subtchallenge/transponder_design/assembly_photos/step_2.jpg

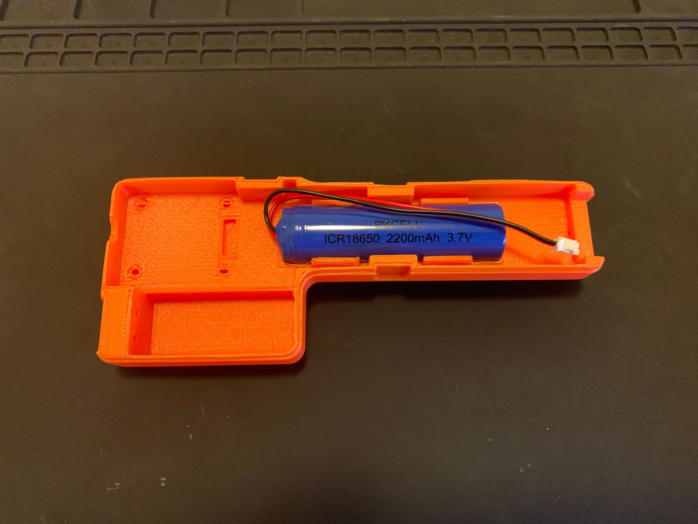
assembly_photos/step_2.jpg
