subtchallenge/transponder_design/assembly_photos/step_3a.jpg

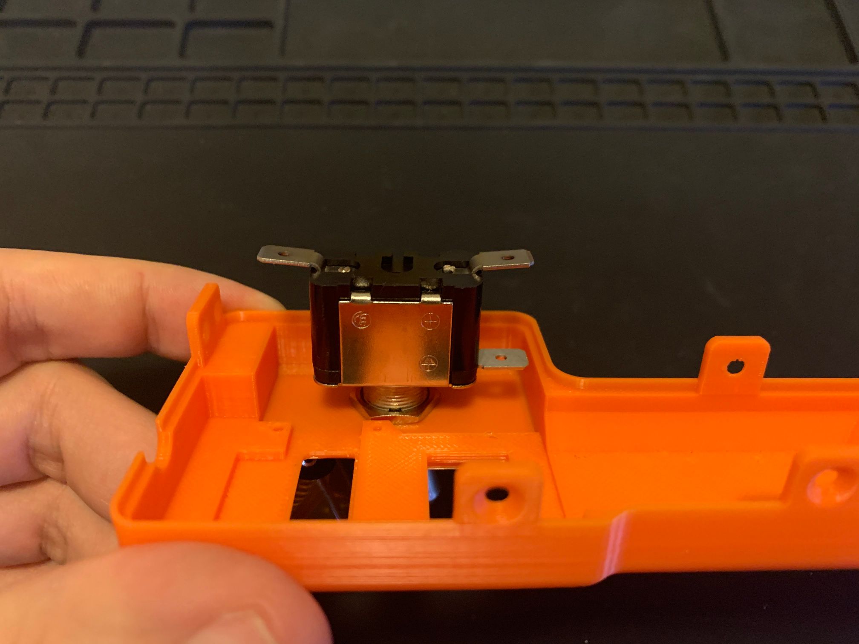
assembly_photos/step_3a.jpg
