subtchallenge/transponder_design/assembly_photos/step_4a.jpg

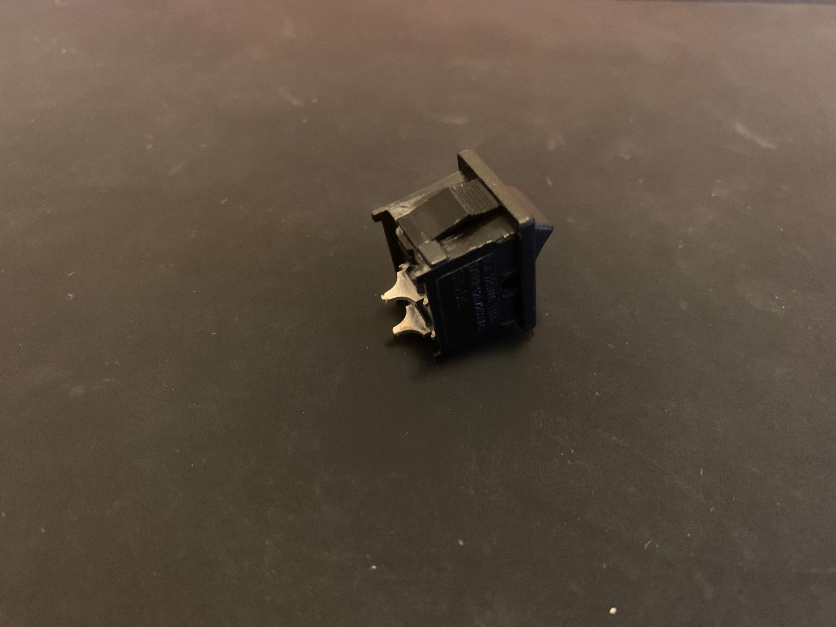
assembly_photos/step_4a.jpg
