subtchallenge/transponder_design/assembly_photos/step_4b.jpg

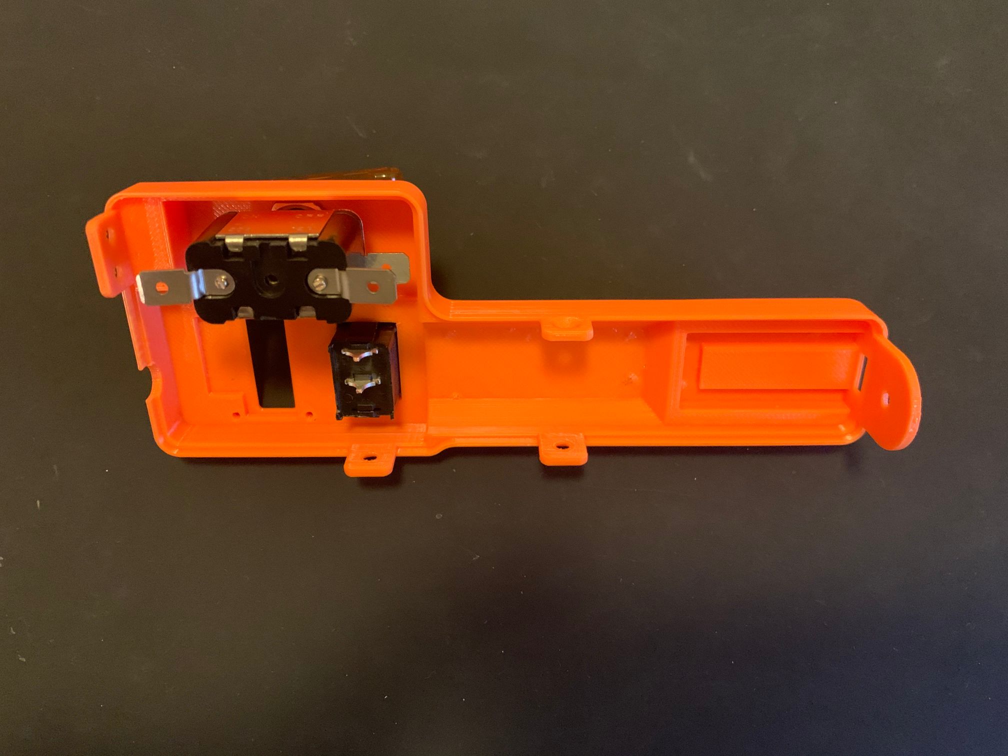
assembly_photos/step_4b.jpg
