subtchallenge/transponder_design/assembly_photos/step_5a.jpg

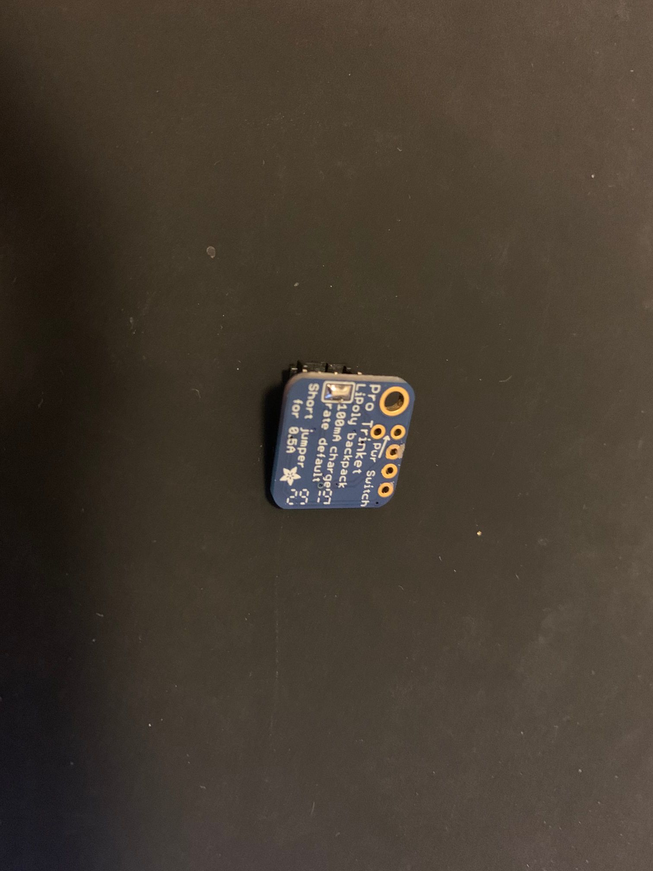
assembly_photos/step_5a.jpg
