subtchallenge/transponder_design/assembly_photos/step_6.jpg

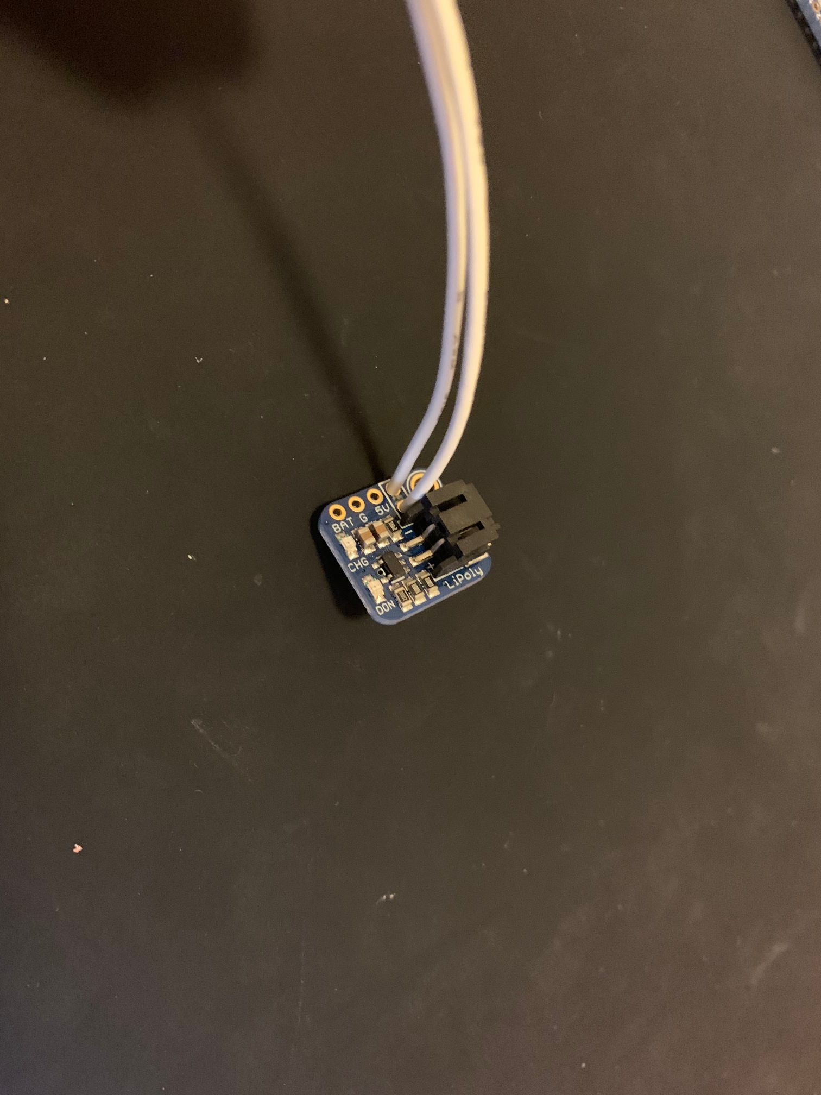
assembly_photos/step_6.jpg
