subtchallenge/transponder_design/assembly_photos/step_7.jpg

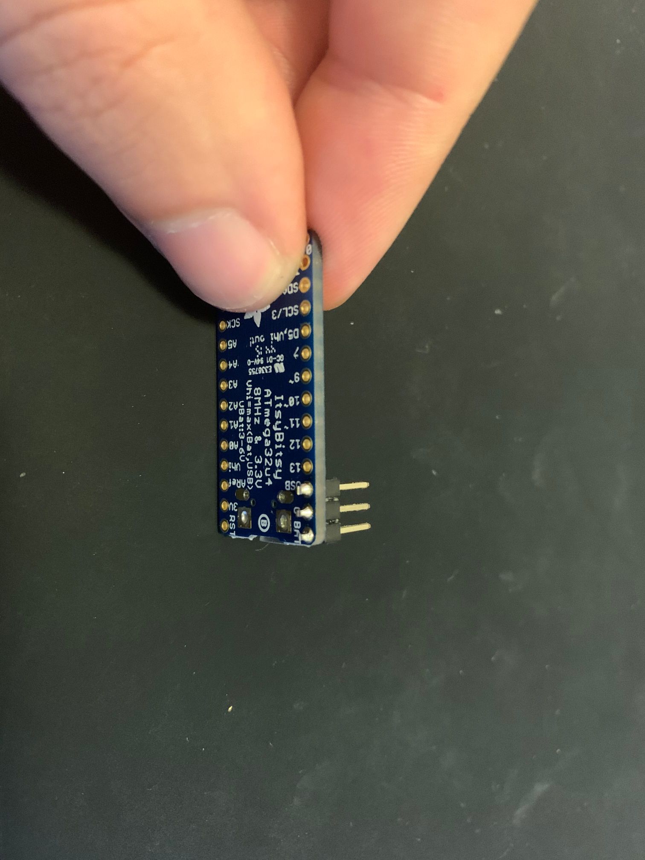
assembly_photos/step_7.jpg
