subtchallenge/transponder_design/assembly_photos/step_8.jpg

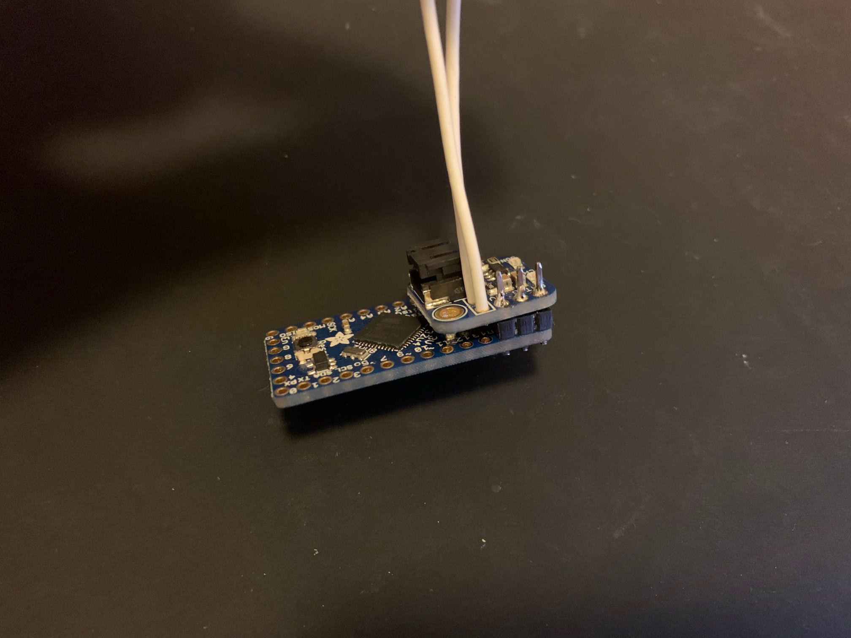
assembly_photos/step_8.jpg
