subtchallenge/transponder_design/assembly_photos/step_9.jpg

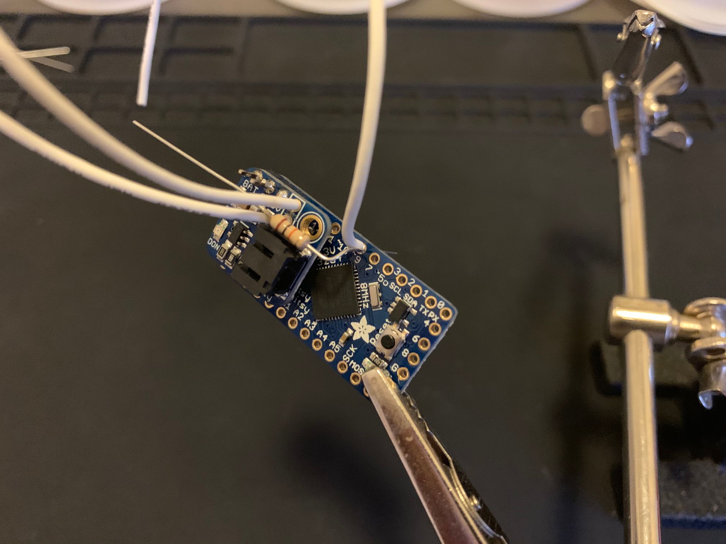
assembly_photos/step_9.jpg
