subtchallenge/transponder_design/assembly_photos/step_10.jpg

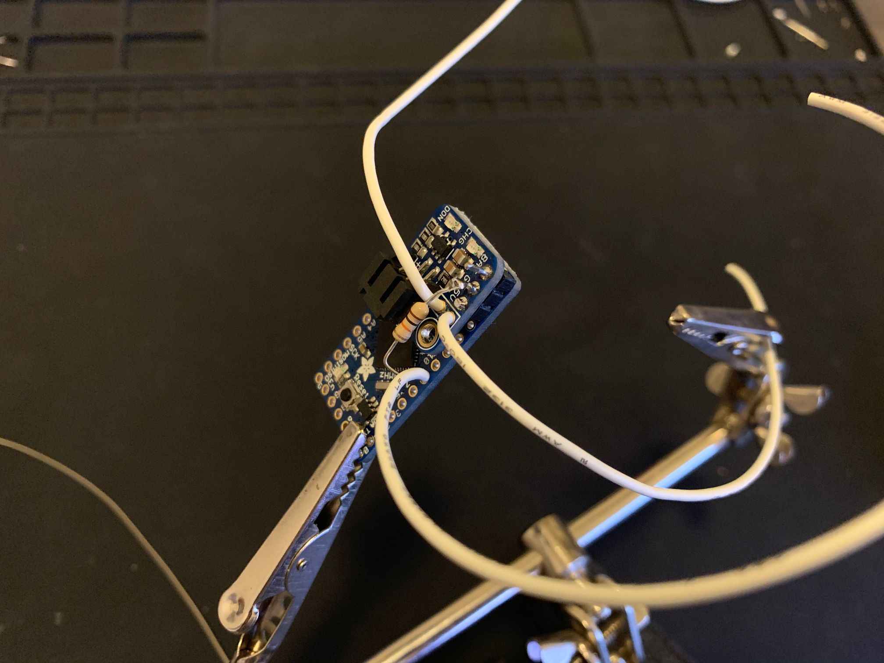
assembly_photos/step_10.jpg
