subtchallenge/transponder_design/assembly_photos/step_11.jpg

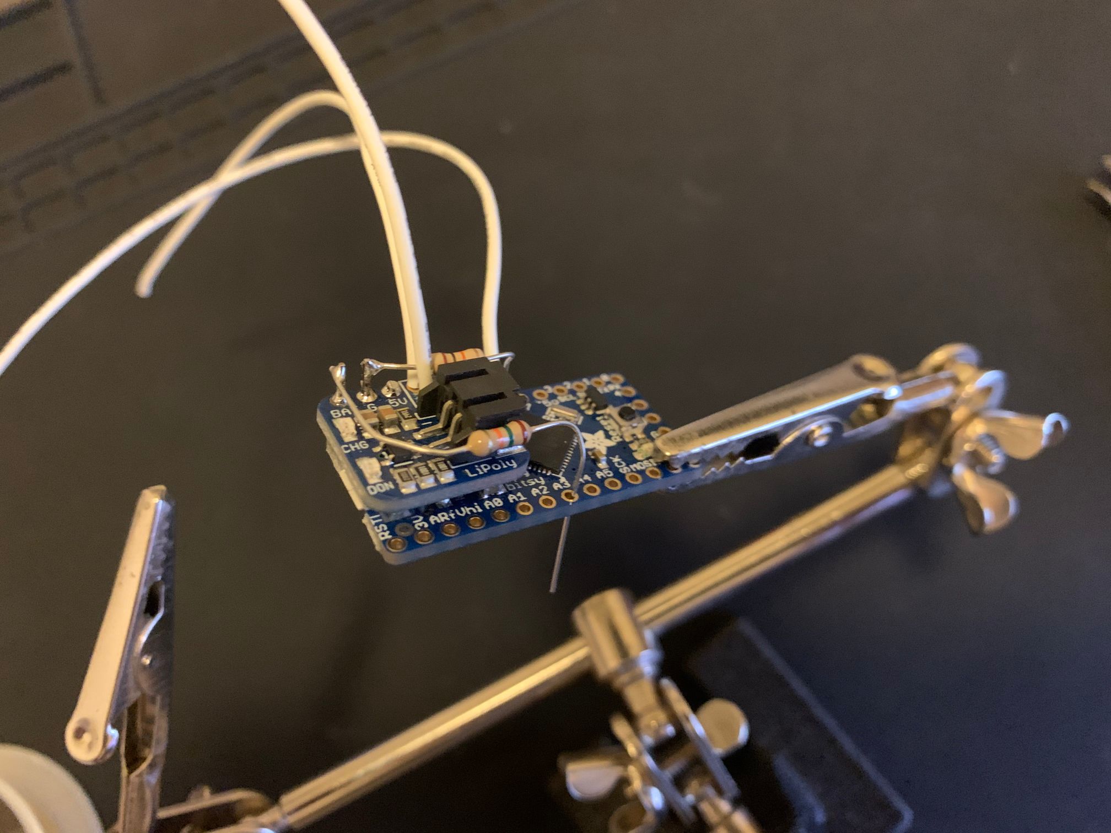
assembly_photos/step_11.jpg
