subtchallenge/transponder_design/assembly_photos/step_12.jpg

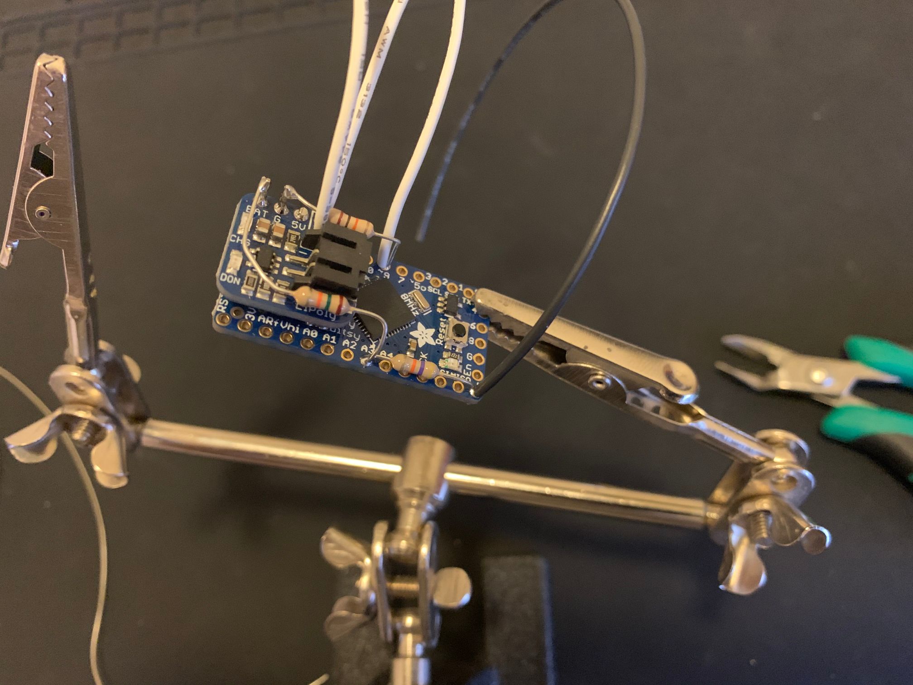
assembly_photos/step_12.jpg
