subtchallenge/transponder_design/assembly_photos/step_13.jpg

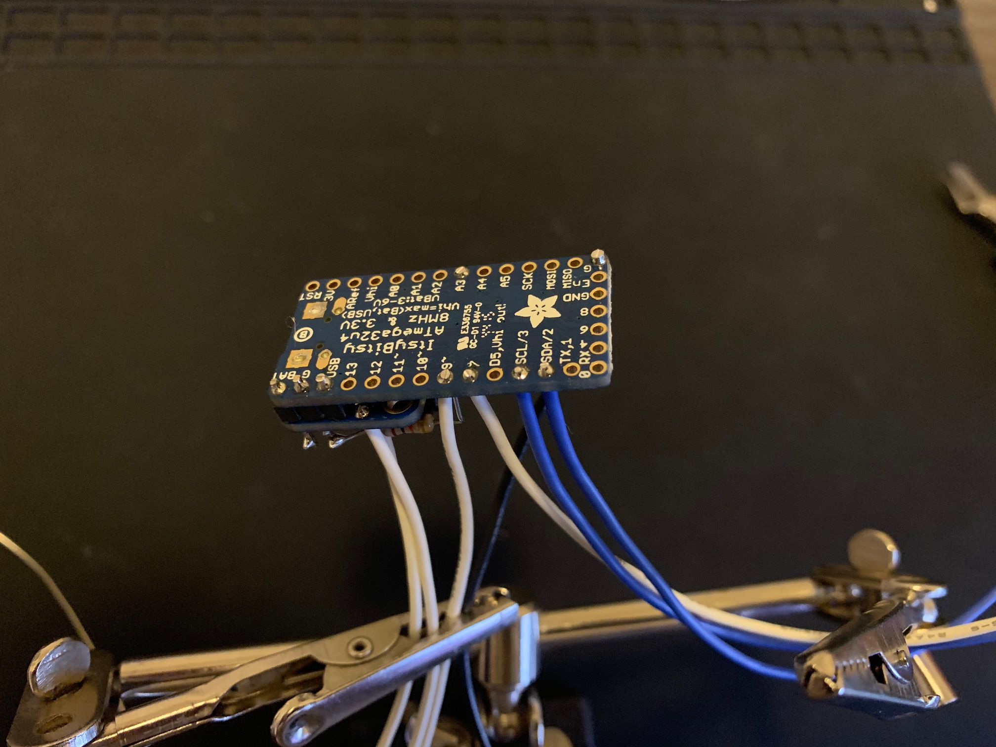
assembly_photos/step_13.jpg
