subtchallenge/transponder_design/assembly_photos/step_14.jpg

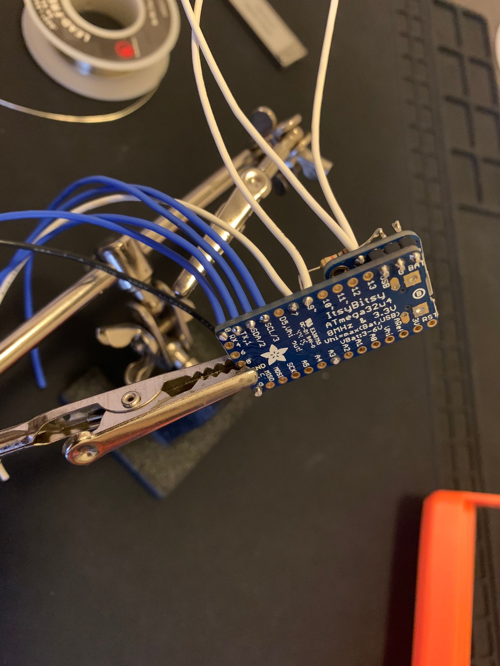
assembly_photos/step_14.jpg
