subtchallenge/transponder_design/assembly_photos/step_15.jpg

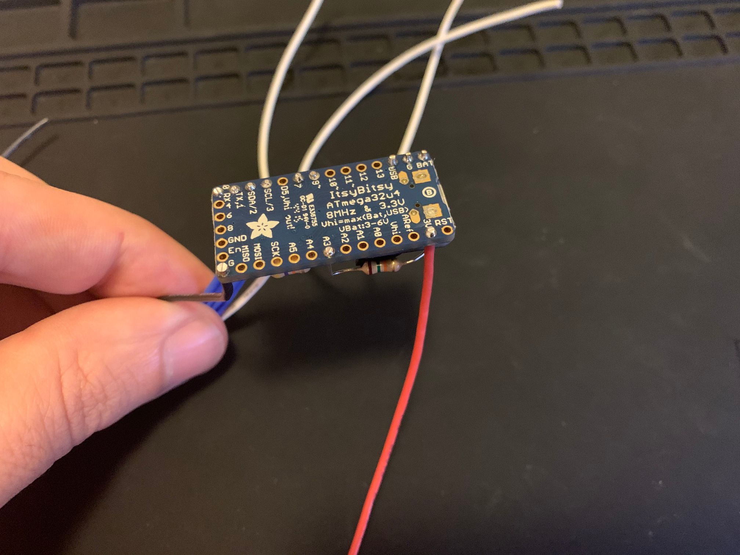
assembly_photos/step_15.jpg
