subtchallenge/transponder_design/assembly_photos/step_16.jpg

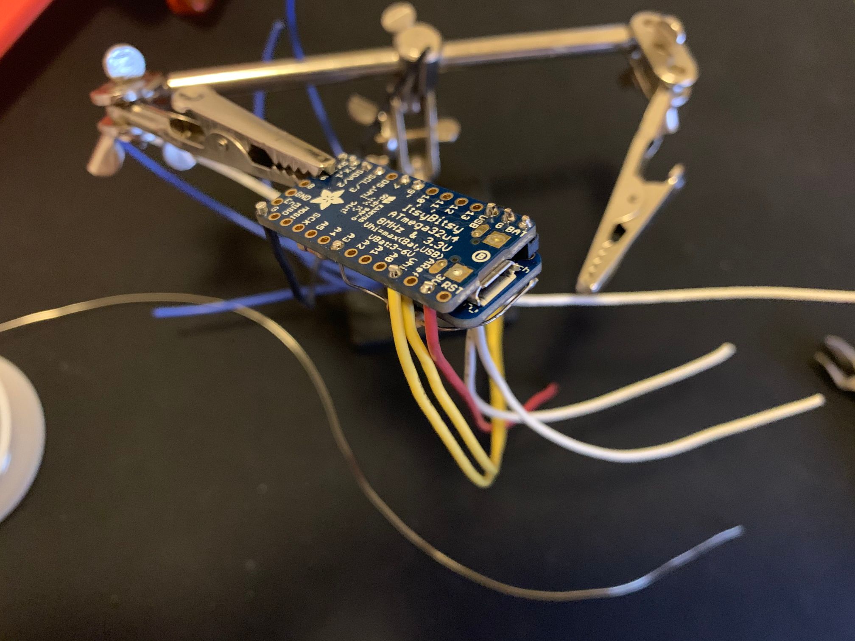
assembly_photos/step_16.jpg
