subtchallenge/transponder_design/assembly_photos/step_18.jpg

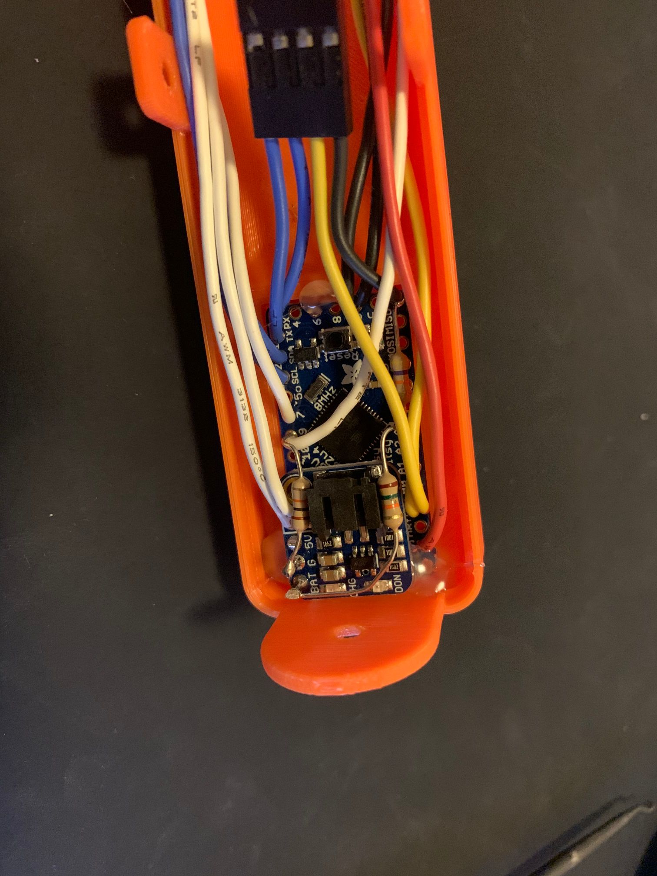
assembly_photos/step_18.jpg
