subtchallenge/transponder_design/assembly_photos/step_19.jpg

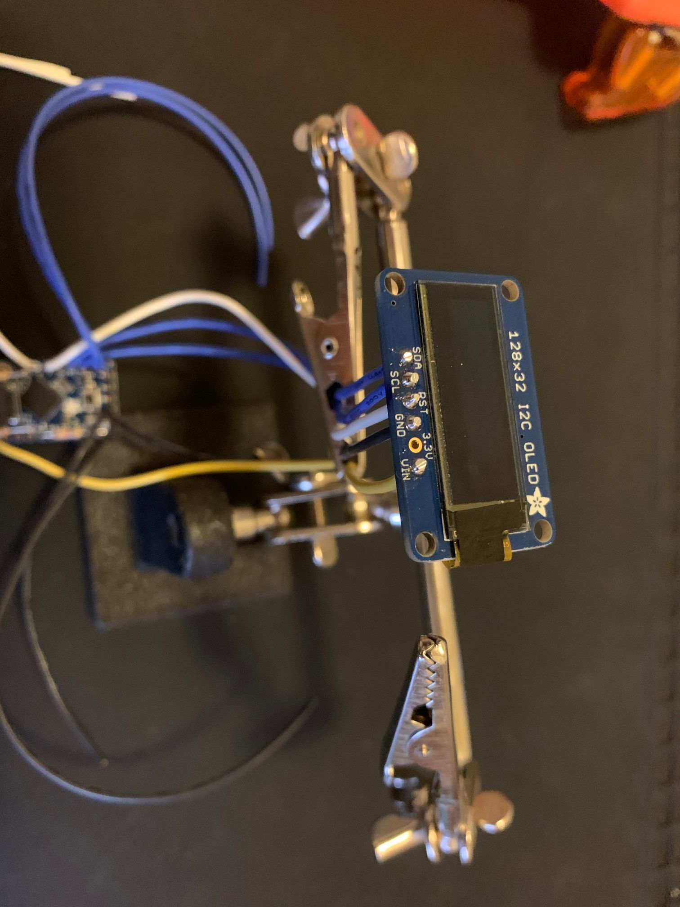
assembly_photos/step_19.jpg
