subtchallenge/transponder_design/assembly_photos/step_21.jpg

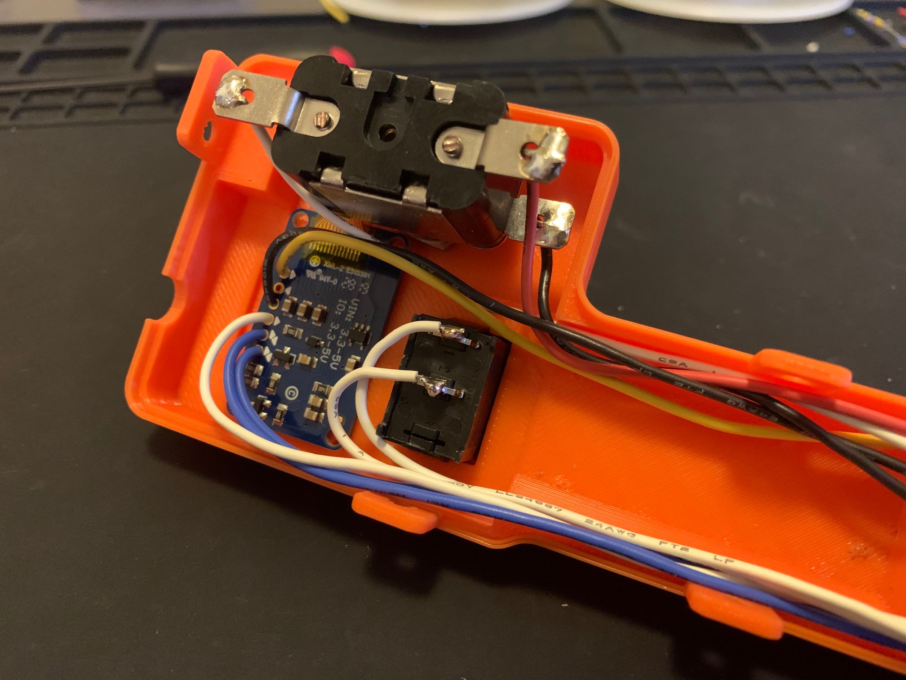
assembly_photos/step_21.jpg
