subtchallenge/transponder_design/assembly_photos/step_22.jpg

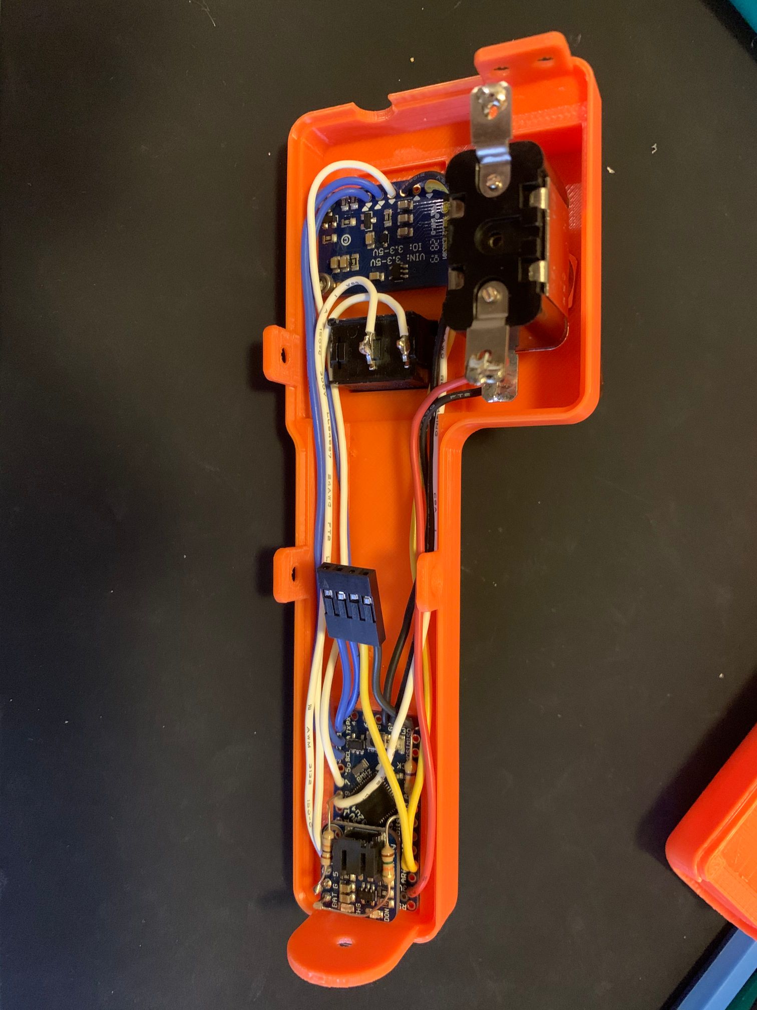
assembly_photos/step_22.jpg
