subtchallenge/transponder_design/assembly_photos/step_23.jpg

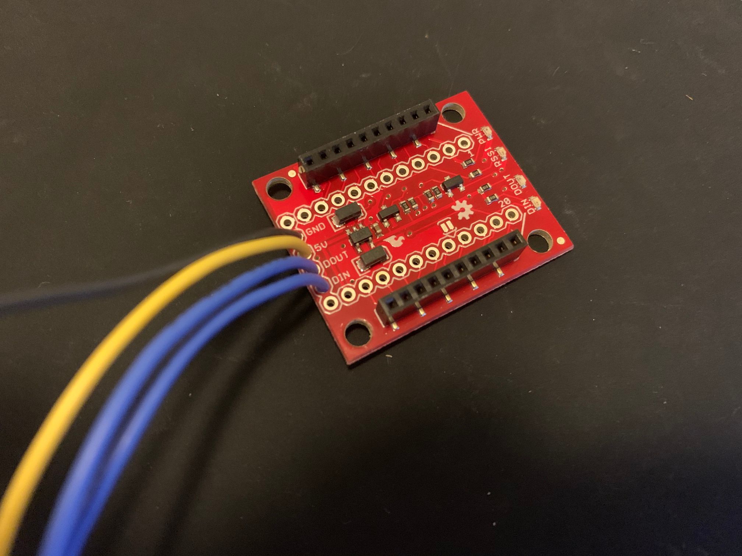
assembly_photos/step_23.jpg
