subtchallenge/transponder_design/assembly_photos/step_24.jpg

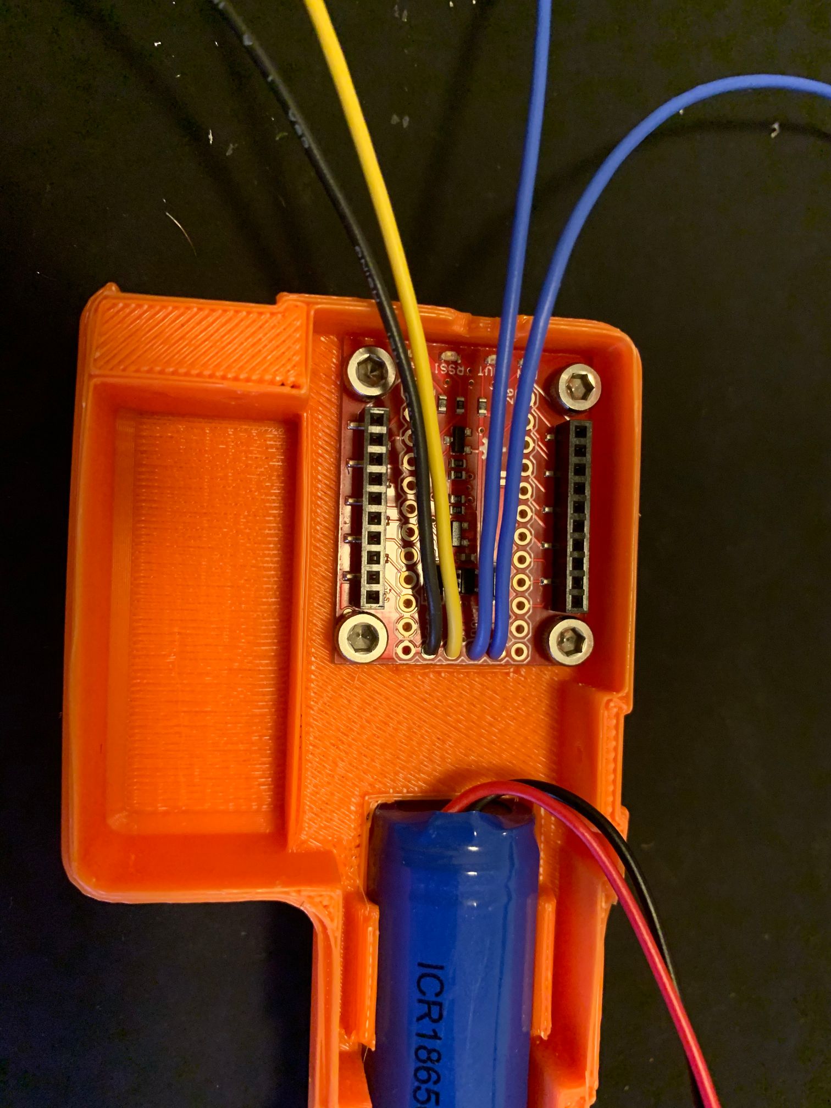
assembly_photos/step_24.jpg
