subtchallenge/transponder_design/assembly_photos/step_25.jpg

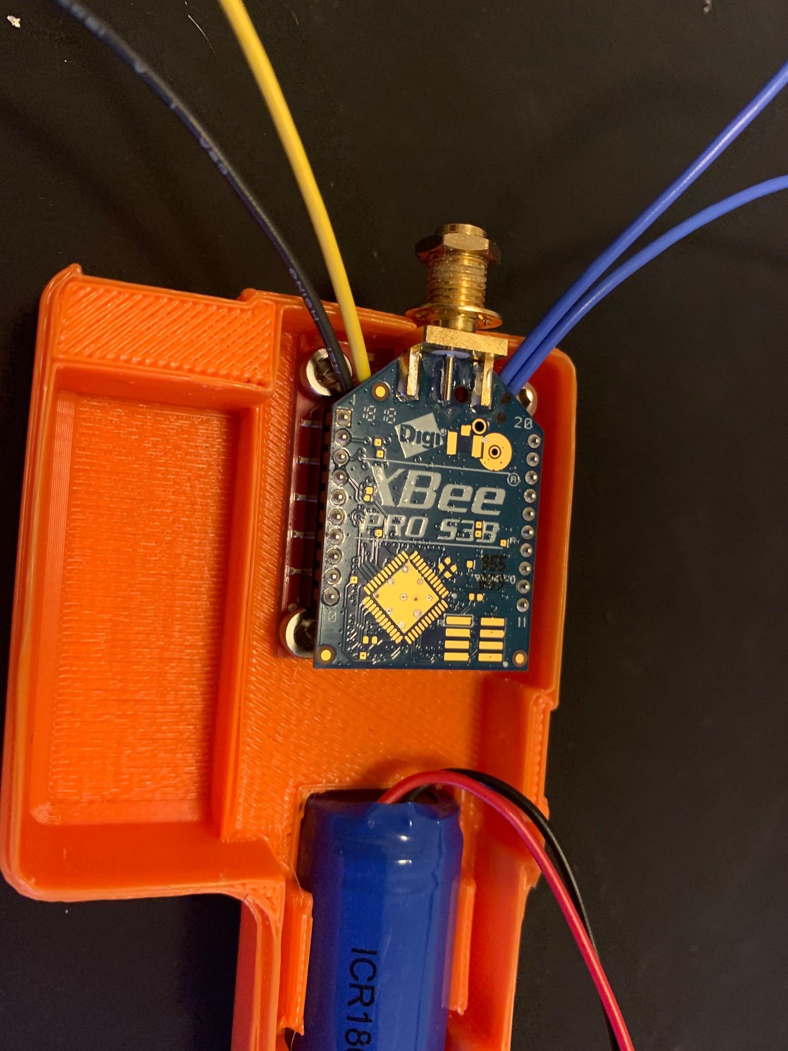
assembly_photos/step_25.jpg
